DPIclimate/enviro-node/electronics/motherboard/enviro-node/parts/connectors/5-pole/2604-3105/2604-3105.stp

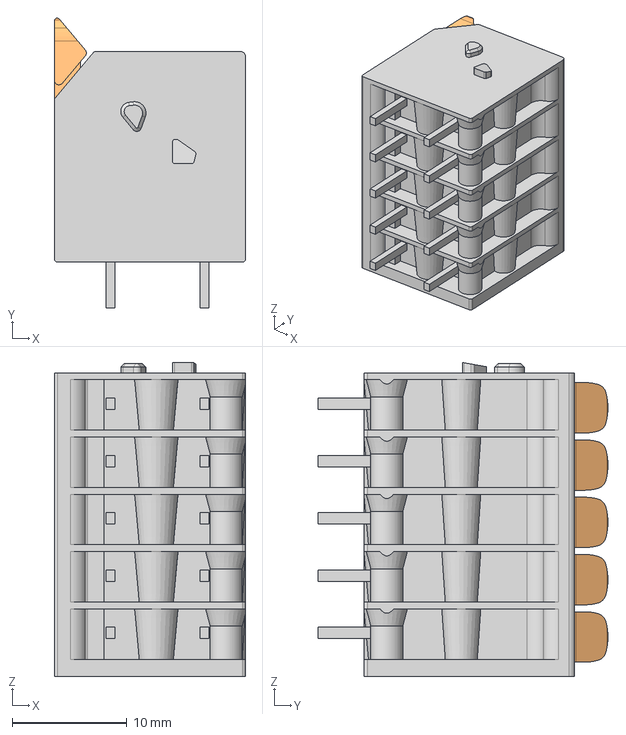
[picture p17: CAD file, 2022-11-16]
electronics/motherboard/enviro-node/parts/connectors/5-pole/2604-3105/2604-3105.stp
16.7 x 25.3 x 27.4 mm
