DPIclimate/enviro-node/electronics/motherboard/enviro-node/parts/connectors/EJ503A/EJ503A.step

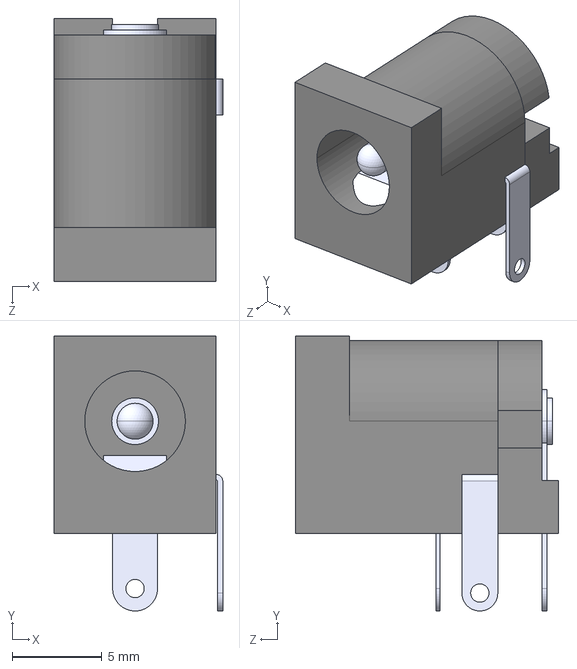
[picture p18: CAD file, 2022-09-02]
electronics/motherboard/enviro-node/parts/connectors/EJ503A/EJ503A.step
9.38 x 15.3 x 14.6 mm
