DPIclimate/enviro-node/electronics/motherboard/enviro-node/parts/connectors/jtag/3221-10-0100-00/3221-10-0100-00.STEP

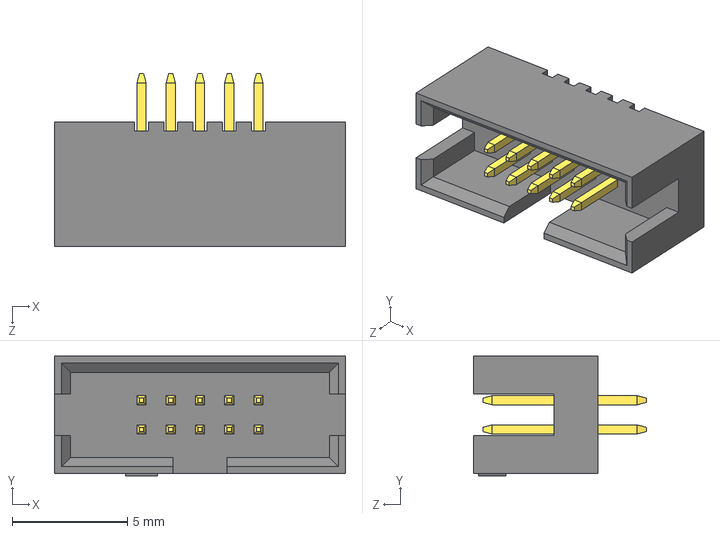
[picture p19: CAD file, 2023-01-09]
electronics/motherboard/enviro-node/parts/connectors/jtag/3221-10-0100-00/3221-10-0100-00.STEP
12.7 x 5.20 x 7.50 mm
