DPIclimate/enviro-node/electronics/motherboard/enviro-node/parts/connectors/nano-sim/SIM8060-6-0-14-00-A/SIM8060-6-0-14-00-A.stp

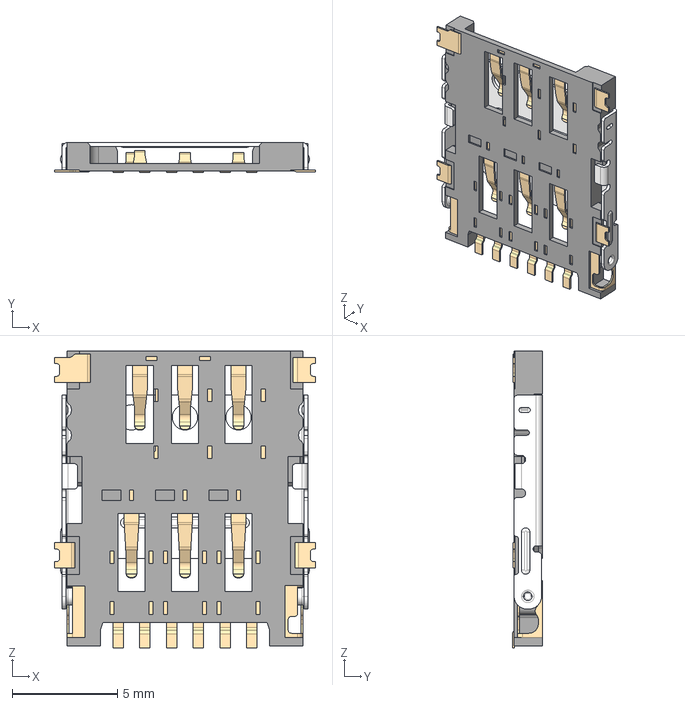
[picture p20: CAD file, 2022-10-10]
electronics/motherboard/enviro-node/parts/connectors/nano-sim/SIM8060-6-0-14-00-A/SIM8060-6-0-14-00-A.stp
12.4 x 1.43 x 14.1 mm
SIM8060-6-0-14-00-A_PART2
SIM8060-6-0-14-00-A_PART1
