DPIclimate/enviro-node/electronics/motherboard/enviro-node/parts/connectors/PCIe/MDT420B03001/MDT420B03001.step

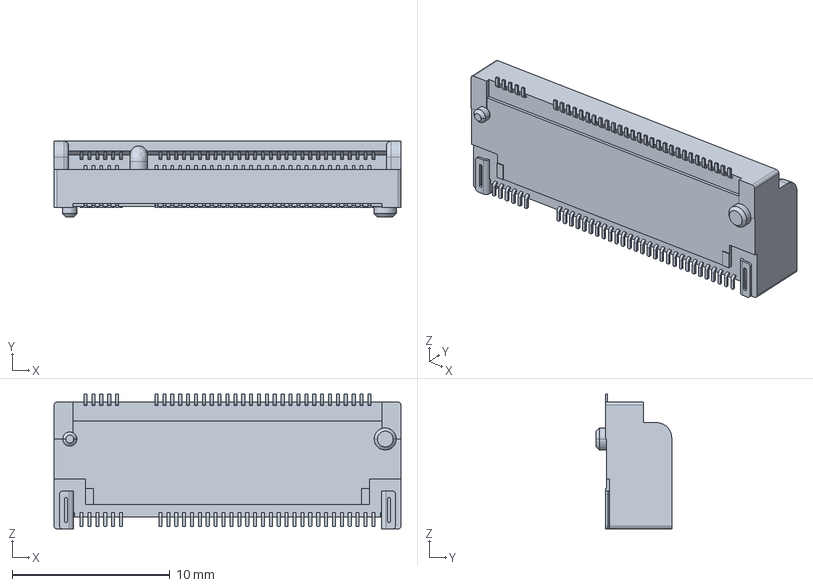
[picture p21: CAD file, 2022-09-12]
electronics/motherboard/enviro-node/parts/connectors/PCIe/MDT420B03001/MDT420B03001.step
22.0 x 4.80 x 8.55 mm
