DPIclimate/enviro-node/electronics/motherboard/enviro-node/parts/connectors/TBP02R2-381-02BE/TBP02R2-381-02BE.step

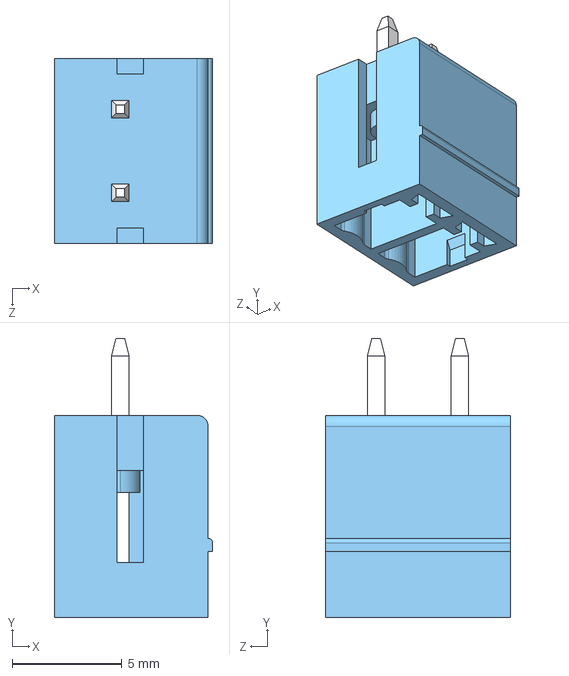
[picture p22: CAD file, 2022-09-15]
electronics/motherboard/enviro-node/parts/connectors/TBP02R2-381-02BE/TBP02R2-381-02BE.step
7.20 x 12.7 x 8.41 mm
