DPIclimate/enviro-node/electronics/motherboard/enviro-node/parts/connectors/TBP02R2-381-03BE/TBP02R2-381-03BE.step

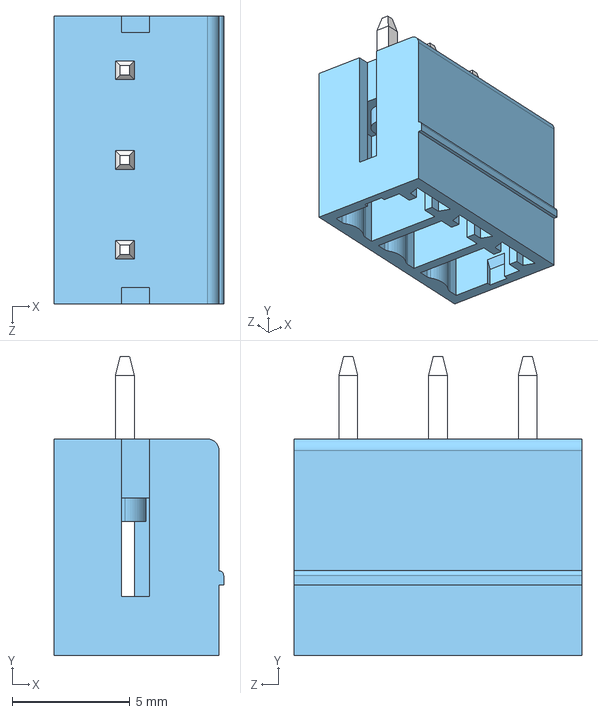
[picture p23: CAD file, 2022-09-15]
electronics/motherboard/enviro-node/parts/connectors/TBP02R2-381-03BE/TBP02R2-381-03BE.step
7.20 x 12.7 x 12.2 mm
