DPIclimate/enviro-node/electronics/motherboard/enviro-node/parts/connectors/TBP02R2-381-04BE/TBP02R2-381-04BE.step

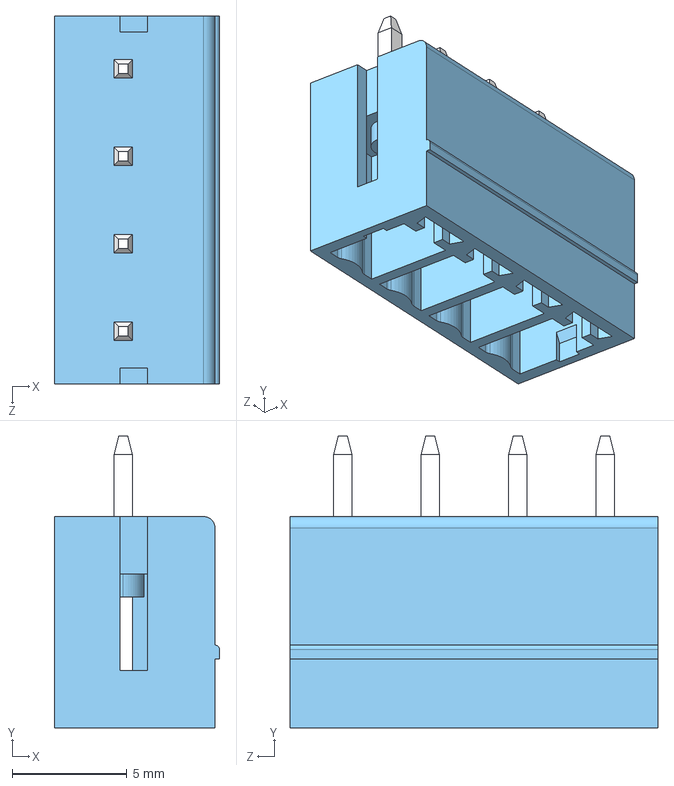
[picture p24: CAD file, 2022-09-02]
electronics/motherboard/enviro-node/parts/connectors/TBP02R2-381-04BE/TBP02R2-381-04BE.step
7.20 x 12.7 x 16.0 mm
