DPIclimate/enviro-node/electronics/motherboard/enviro-node/parts/connectors/usb-c/USB4070-30-C/USB4070-30-C.step

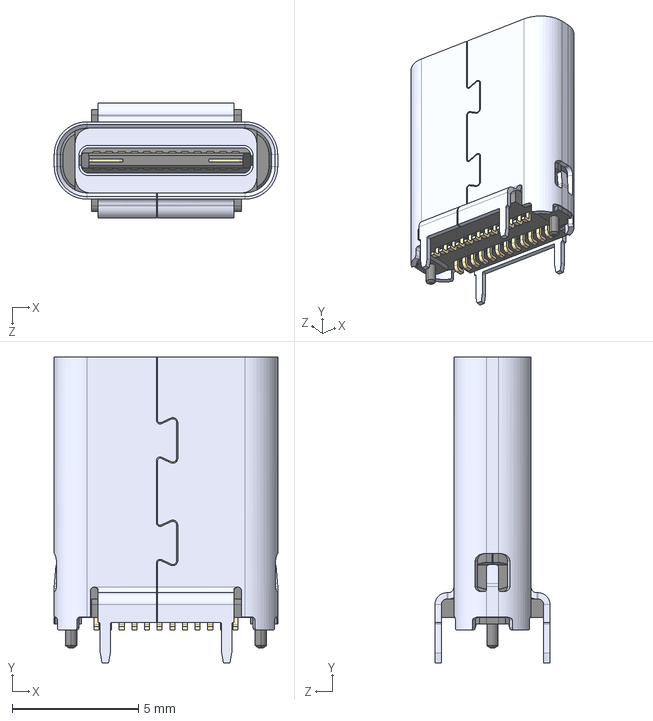
[picture p25: CAD file, 2022-09-13]
electronics/motherboard/enviro-node/parts/connectors/usb-c/USB4070-30-C/USB4070-30-C.step
8.84 x 12.1 x 4.55 mm
