DPIclimate/enviro-node/electronics/motherboard/enviro-node/parts/connectors/usb-c/USB4145-03-0230-C_REVA/USB4145-03-0070-C.stp

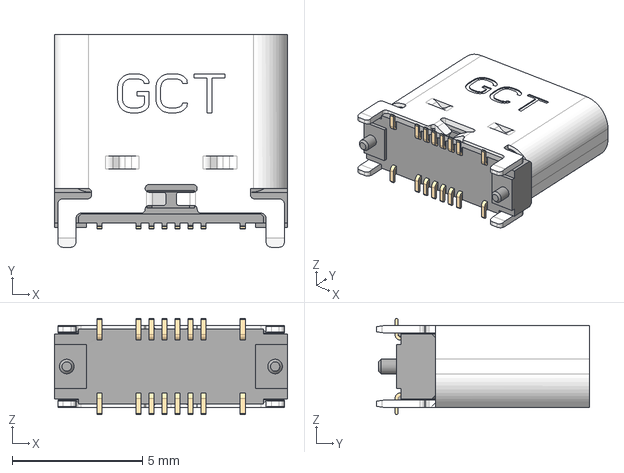
[picture p26: CAD file, 2022-10-10]
electronics/motherboard/enviro-node/parts/connectors/usb-c/USB4145-03-0230-C_REVA/USB4145-03-0070-C.stp
8.95 x 8.16 x 3.69 mm
USB4145-03-0070-C_PART2
USB4145-03-0070-C_PART1
