DPIclimate/enviro-node/electronics/motherboard/enviro-node/parts/diodes/clamping/AOZ8904CIL/SOT-23-6_AOS.step

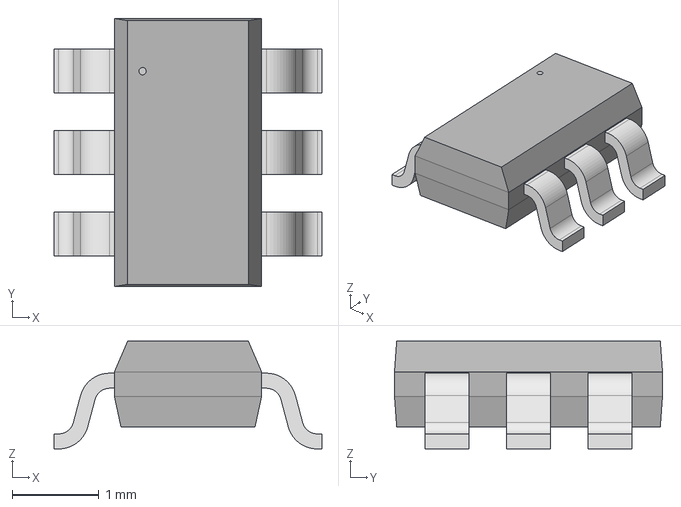
[picture p27: CAD file, 2022-10-10]
electronics/motherboard/enviro-node/parts/diodes/clamping/AOZ8904CIL/SOT-23-6_AOS.step
3.10 x 3.10 x 1.25 mm
