DPIclimate/enviro-node/electronics/motherboard/enviro-node/parts/diodes/MBRS340/MBRS340.step

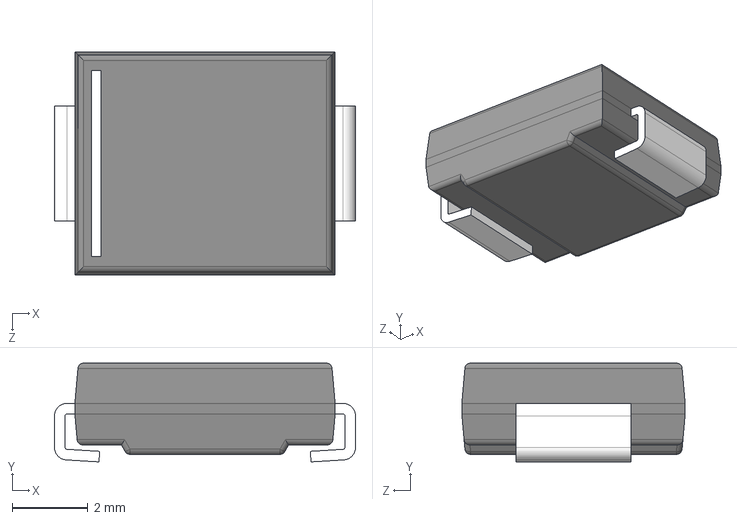
[picture p28: CAD file, 2022-09-02]
electronics/motherboard/enviro-node/parts/diodes/MBRS340/MBRS340.step
7.95 x 2.61 x 5.90 mm
