DPIclimate/enviro-node/electronics/motherboard/enviro-node/parts/diodes/SM5817PL/SODFL3718X108N.step

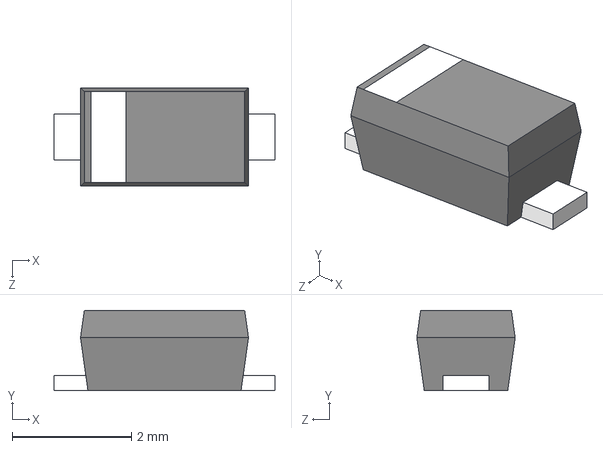
[picture p29: CAD file, 2022-09-02]
electronics/motherboard/enviro-node/parts/diodes/SM5817PL/SODFL3718X108N.step
3.71 x 1.35 x 1.65 mm
