DPIclimate/enviro-node/electronics/motherboard/enviro-node/parts/diodes/SS34LW_RVG/SS34LW_RVG.step

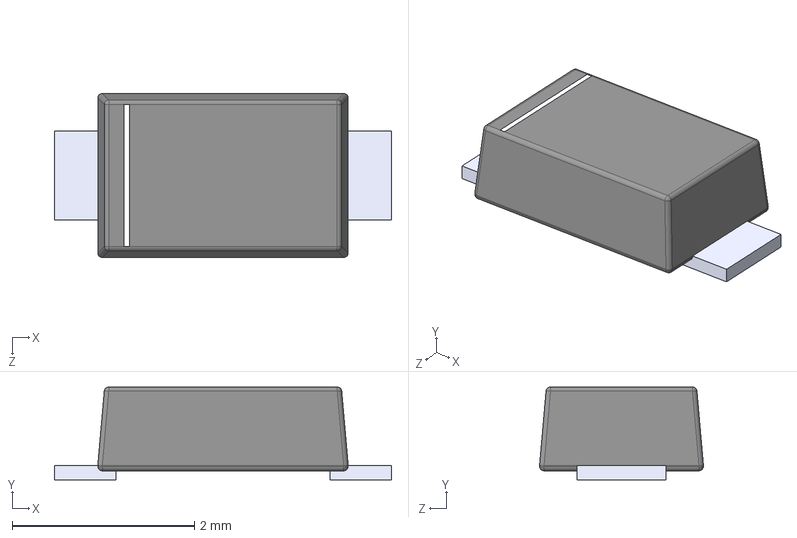
[picture p30: CAD file, 2022-09-13]
electronics/motherboard/enviro-node/parts/diodes/SS34LW_RVG/SS34LW_RVG.step
3.70 x 1.02 x 1.80 mm
