DPIclimate/enviro-node/electronics/motherboard/enviro-node/parts/ferrite-beads/FBMH2012HM221-TV/FBMH2012HM221-TV.step

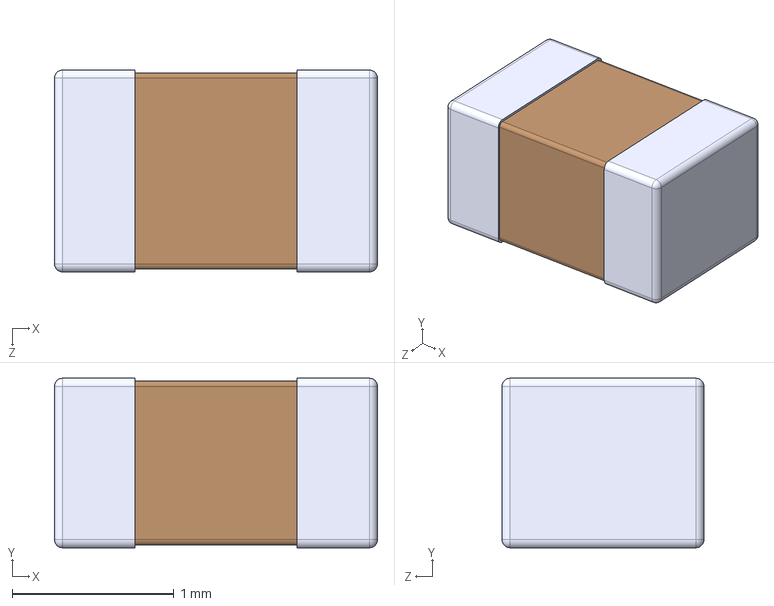
[picture p31: CAD file, 2022-10-10]
electronics/motherboard/enviro-node/parts/ferrite-beads/FBMH2012HM221-TV/FBMH2012HM221-TV.step
2.00 x 1.05 x 1.25 mm
