DPIclimate/enviro-node/electronics/motherboard/enviro-node/parts/inductors/CBC2518T100M/CBC2518T100M.step

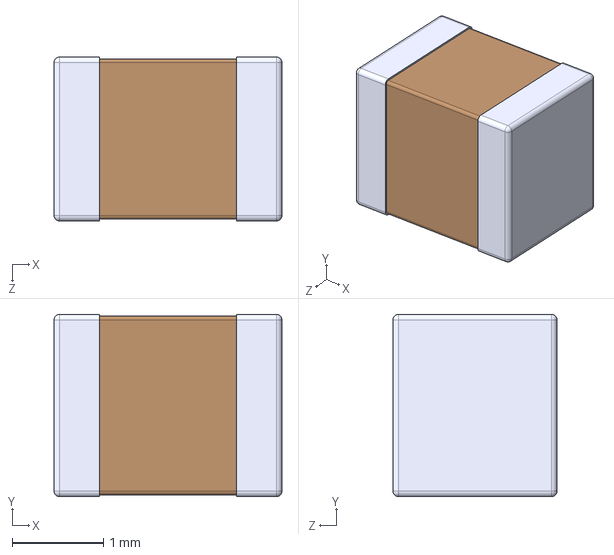
[picture p32: CAD file, 2022-09-02]
electronics/motherboard/enviro-node/parts/inductors/CBC2518T100M/CBC2518T100M.step
2.50 x 2.00 x 1.80 mm
