DPIclimate/enviro-node/electronics/motherboard/enviro-node/parts/inductors/LQH43CN100K03L/LQH43CN100K03L.step

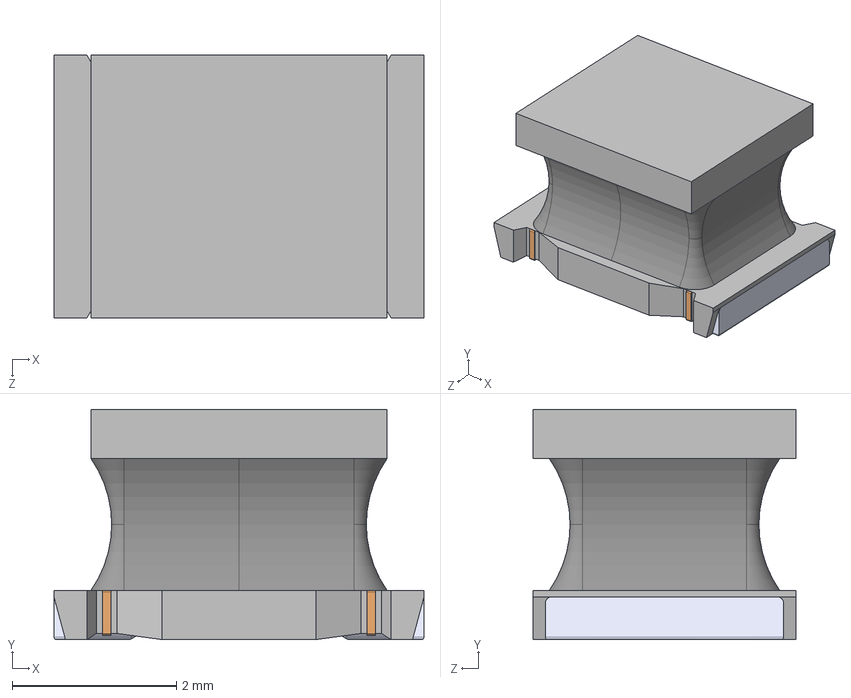
[picture p33: CAD file, 2022-10-12]
electronics/motherboard/enviro-node/parts/inductors/LQH43CN100K03L/LQH43CN100K03L.step
4.50 x 2.80 x 3.20 mm
