DPIclimate/enviro-node/electronics/motherboard/enviro-node/parts/inductors/SRP4020TA-5R6M/IND2_SRP4020TA-R56M_BRN.step

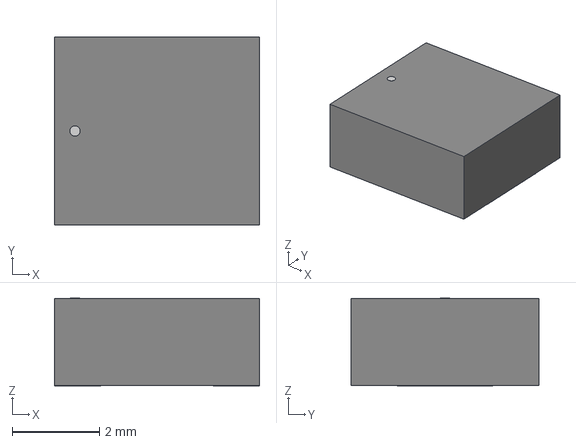
[picture p34: CAD file, 2022-11-08]
electronics/motherboard/enviro-node/parts/inductors/SRP4020TA-5R6M/IND2_SRP4020TA-R56M_BRN.step
4.70 x 4.32 x 2.01 mm
