DPIclimate/enviro-node/electronics/motherboard/enviro-node/parts/leds/BB-2020BGR-TRB/BB-2020BGR-TRB.step

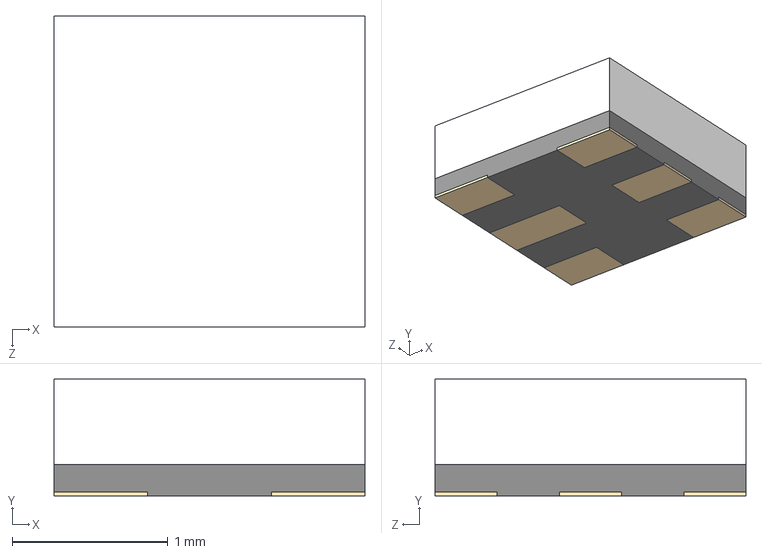
[picture p35: CAD file, 2022-09-12]
electronics/motherboard/enviro-node/parts/leds/BB-2020BGR-TRB/BB-2020BGR-TRB.step
2.00 x 0.75 x 2.00 mm
