DPIclimate/enviro-node/electronics/motherboard/enviro-node/parts/level-shifter/NVT2006PW/TSSOP16_SOT403-1_NXP.step

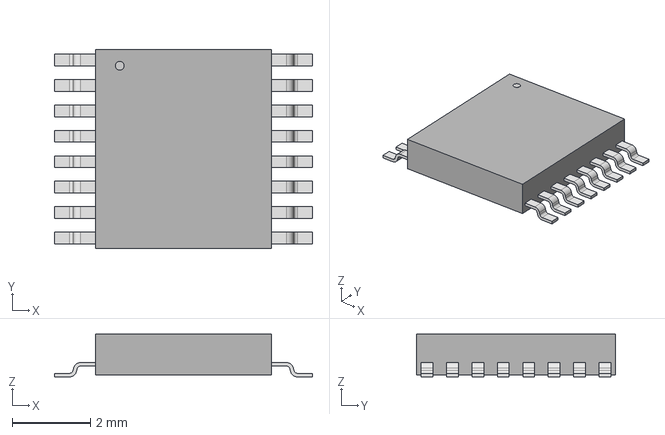
[picture p36: CAD file, 2022-10-10]
electronics/motherboard/enviro-node/parts/level-shifter/NVT2006PW/TSSOP16_SOT403-1_NXP.step
6.60 x 5.11 x 1.09 mm
