DPIclimate/enviro-node/electronics/motherboard/enviro-node/parts/microcontrollers/ESP32-WROOM-32E__16MB_/ESP32-WROOM-32E__16MB_.step

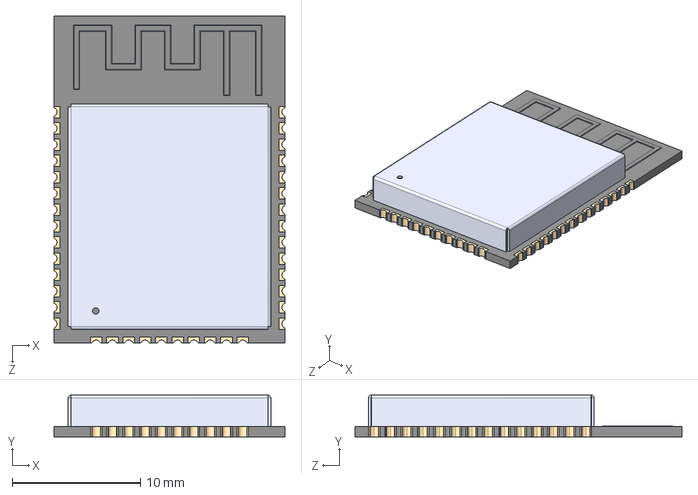
[picture p37: CAD file, 2022-11-02]
electronics/motherboard/enviro-node/parts/microcontrollers/ESP32-WROOM-32E__16MB_/ESP32-WROOM-32E__16MB_.step
18.0 x 3.25 x 25.5 mm
