DPIclimate/enviro-node/electronics/motherboard/enviro-node/parts/mosfets/p-channel/SSM3J340R-LF/SOT-23F.step

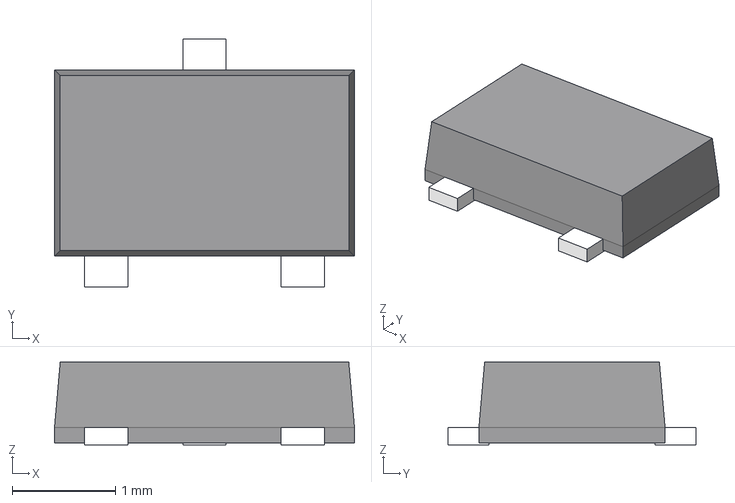
[picture p38: CAD file, 2023-01-09]
electronics/motherboard/enviro-node/parts/mosfets/p-channel/SSM3J340R-LF/SOT-23F.step
2.90 x 2.40 x 0.8 mm
