DPIclimate/enviro-node/electronics/motherboard/enviro-node/parts/ocillators/ABS05-32.768KHZ-9-T/ABS05-32.768KHZ-9-T.step

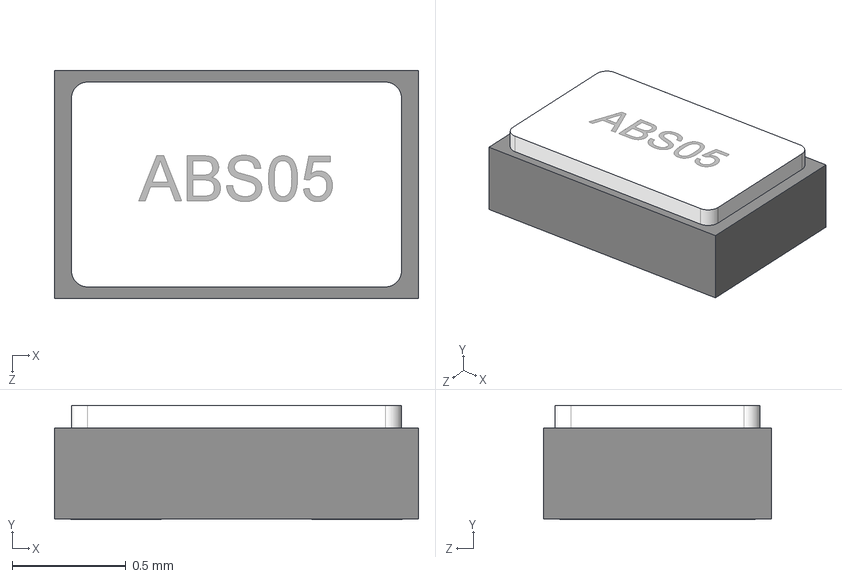
[picture p39: CAD file, 2022-09-12]
electronics/motherboard/enviro-node/parts/ocillators/ABS05-32.768KHZ-9-T/ABS05-32.768KHZ-9-T.step
1.60 x 0.503 x 1.00 mm
