DPIclimate/enviro-node/electronics/motherboard/enviro-node/parts/ocillators/ABS07AIG-32.768KHZ-T/ABS07AIG-32.768KHZ-T.step

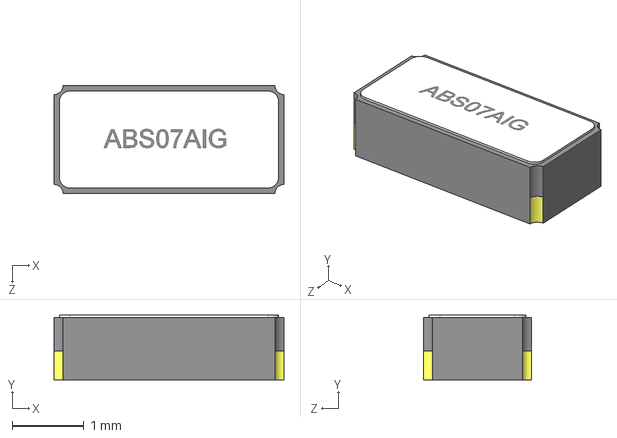
[picture p40: CAD file, 2022-11-02]
electronics/motherboard/enviro-node/parts/ocillators/ABS07AIG-32.768KHZ-T/ABS07AIG-32.768KHZ-T.step
3.20 x 0.901 x 1.50 mm
