DPIclimate/enviro-node/electronics/motherboard/enviro-node/parts/piezo-buzzers/PS1240P02BT/PS1240P02BT.step

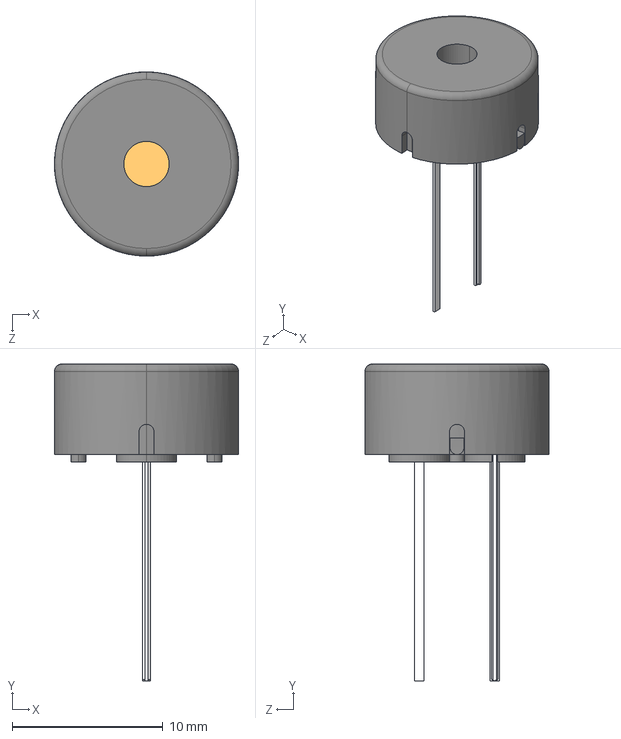
[picture p41: CAD file, 2022-11-02]
electronics/motherboard/enviro-node/parts/piezo-buzzers/PS1240P02BT/PS1240P02BT.step
12.2 x 21.0 x 12.2 mm
