DPIclimate/enviro-node/electronics/motherboard/enviro-node/parts/switches/dip/DS04-254-2-02BK-SMT/DS04-254-2-02BK-SMT.step

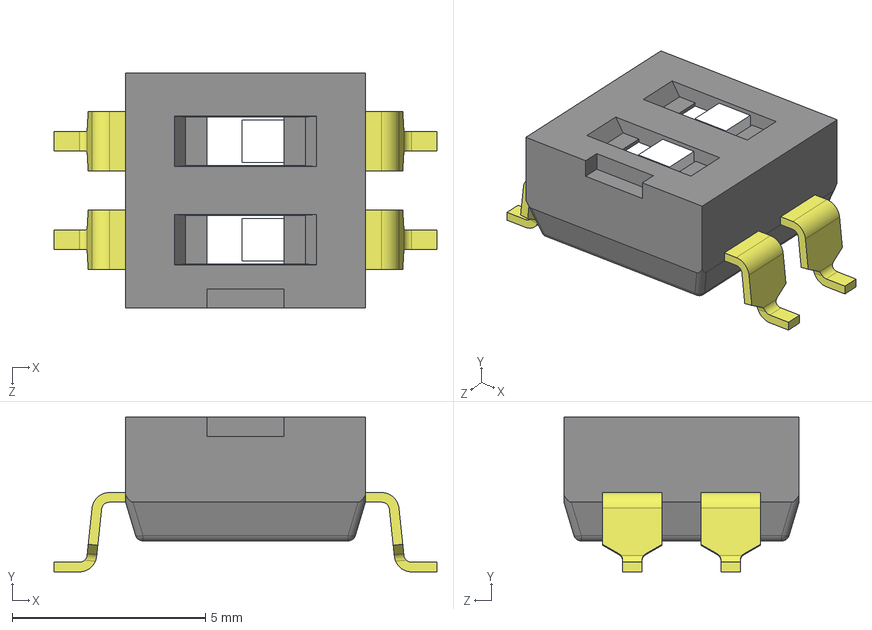
[picture p42: CAD file, 2022-09-13]
electronics/motherboard/enviro-node/parts/switches/dip/DS04-254-2-02BK-SMT/DS04-254-2-02BK-SMT.step
9.90 x 4.00 x 6.08 mm
