DPIclimate/enviro-node/electronics/motherboard/enviro-node/parts/transistors/AOD417/AOD417.step

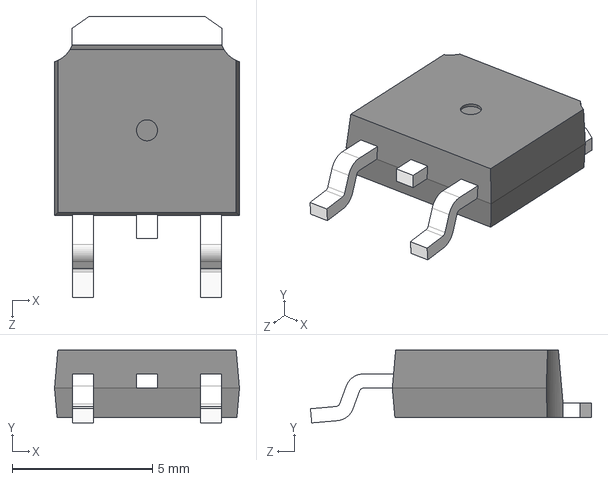
[picture p43: CAD file, 2022-09-02]
electronics/motherboard/enviro-node/parts/transistors/AOD417/AOD417.step
6.60 x 2.60 x 10.0 mm
