DPIclimate/enviro-node/electronics/motherboard/enviro-node/parts/voltage-regulators/MIC2145BMM/MIC2145BMM.step

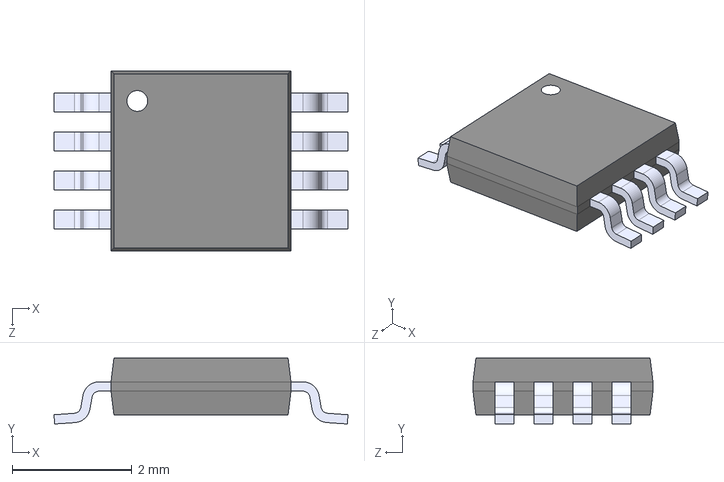
[picture p44: CAD file, 2022-09-02]
electronics/motherboard/enviro-node/parts/voltage-regulators/MIC2145BMM/MIC2145BMM.step
4.90 x 1.10 x 3.00 mm
