DPIclimate/enviro-node/electronics/motherboard/enviro-node/parts/voltage-regulators/MIC2288YD5-TR/MIC2288YD5-TR.step

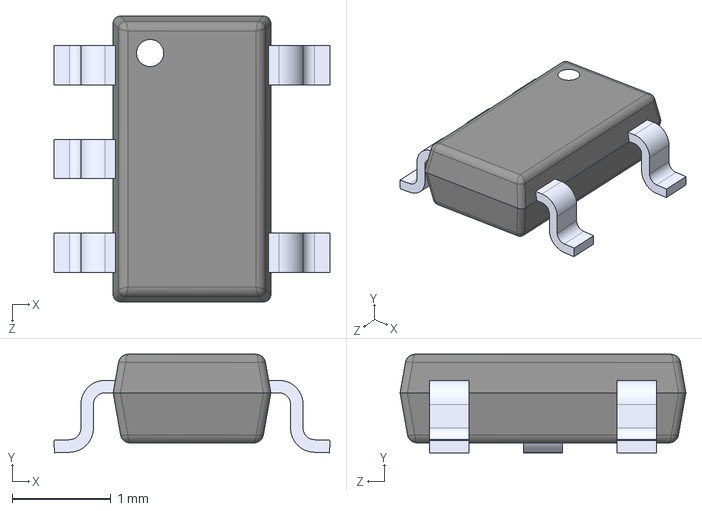
[picture p45: CAD file, 2022-10-12]
electronics/motherboard/enviro-node/parts/voltage-regulators/MIC2288YD5-TR/MIC2288YD5-TR.step
2.80 x 1.00 x 2.90 mm
