DPIclimate/enviro-node/electronics/motherboard/enviro-node/parts/voltage-regulators/XC6215B332MR-G/SOT-25_TOR.step

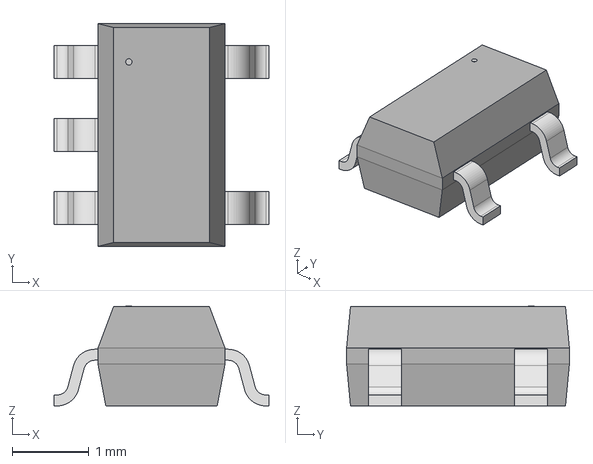
[picture p46: CAD file, 2022-11-02]
electronics/motherboard/enviro-node/parts/voltage-regulators/XC6215B332MR-G/SOT-25_TOR.step
2.79 x 2.90 x 1.30 mm
