DPIclimate/enviro-node/cad/PVC WB board holder final.stl

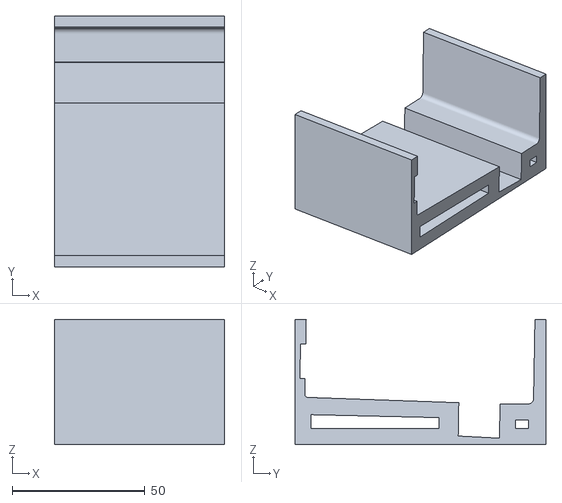
[picture p47: CAD file, 2023-05-02]
cad/PVC WB board holder final.stl
64.0 x 94.3 x 47.2
