DPIclimate/enviro-node/cad/Breakoutbox holder Final.stl

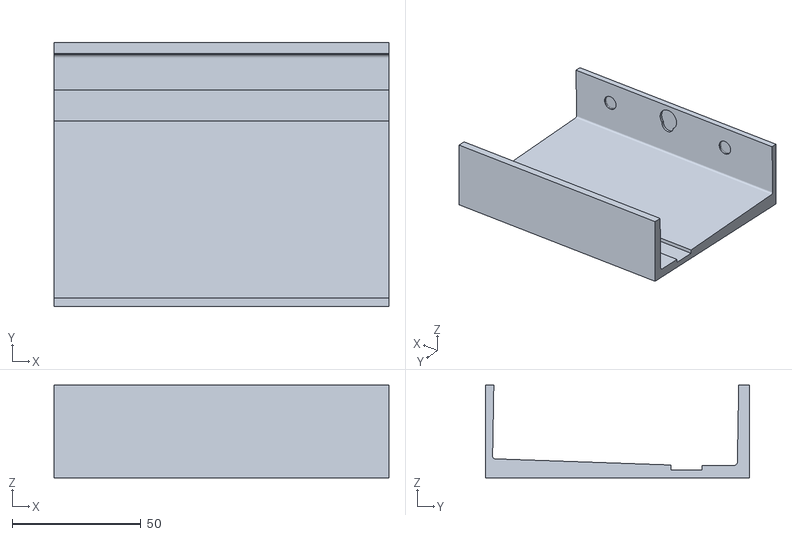
[picture p48: CAD file, 2023-05-02]
cad/Breakoutbox holder Final.stl
130.0 x 102.6 x 36.0
