DPIclimate/enviro-node/firmware/wombat/src/ntp.cpp

#include <Arduino.h>
#include <time.h> // Note: this is the standard c time library, not Time.h
#include "SparkFun_u-blox_SARA-R5_Arduino_Library.h"

#define TAG "ntp"

// Get the time from NTP
// This code is based heavily on:
// https://docs.arduino.cc/tutorials/mkr-nb-1500/mkr-nb-library-examples#mkr-nb-gprs-udp-ntp-client
// Many thanks to: Michael Margolis, Tom Igoe, Arturo Guadalupi, et al

// NTP Server
const char* ntpServer = "au.pool.ntp.org";               // The Network Time Protocol Server
//const char* ntpServer = "africa.pool.ntp.org";        // The Network Time Protocol Server
//const char* ntpServer = "asia.pool.ntp.org";          // The Network Time Protocol Server
//const char* ntpServer = "europe.pool.ntp.org";        // The Network Time Protocol Server
//const char* ntpServer = "north-america.pool.ntp.org"; // The Network Time Protocol Server
//const char* ntpServer = "oceania.pool.ntp.org";       // The Network Time Protocol Server
//const char* ntpServer = "south-america.pool.ntp.org"; // The Network Time Protocol Server

//=-=-=-=-=-=-=-=-=-=-=-=-=-=-=-=-=-=-=-=-=-=-=-=-=-=-=-=-=-=-=-=-=-=-=-=-=-=-=-=-=-=-=-=-=

bool getNTPTime(SARA_R5 &r5) {
    int serverPort = 123; //NTP requests are to port 123

    // Set up the packetBuffer for the NTP request
    const int NTP_PACKET_SIZE = 48; // NTP time stamp is in the first 48 bytes of the message
    byte packetBuffer[NTP_PACKET_SIZE]; //buffer to hold incoming and outgoing packets

    // set all bytes in the buffer to 0
    memset(packetBuffer, 0, NTP_PACKET_SIZE);

    // Initialize values needed to form NTP request. The client request only needs to set version numbers & mode.
    packetBuffer[0]  = 0b00000000;  // LI 0
    packetBuffer[0] |= 0b00100000;  // Version 4
    packetBuffer[0] |= 0b00000011;  // Mode 3, client
    //=-=-=-=-=-=-=-=-=-=-=-=-=-=-=-=-=-=-=-=-=-=-=-=-=-=-=-=-=-=-=-=-=-=-=-=-=-=-=-=-=-=-=-=-=

    // Allocate a UDP socket to talk to the NTP server

    int socketNum = r5.socketOpen(SARA_R5_UDP);
    if (socketNum == -1) {
        ESP_LOGE(TAG, "socketOpen failed");
        return false;
    }

    ESP_LOGI(TAG, "using socket %u", socketNum);

    //=-=-=-=-=-=-=-=-=-=-=-=-=-=-=-=-=-=-=-=-=-=-=-=-=-=-=-=-=-=-=-=-=-=-=-=-=-=-=-=-=-=-=-=-=

    // Send the request - NTP uses UDP

    if (r5.socketWriteUDP(socketNum, ntpServer, serverPort, (const char *)&packetBuffer, NTP_PACKET_SIZE) != SARA_R5_SUCCESS) {
        ESP_LOGE(TAG, "socketWrite failed");
        r5.socketClose(socketNum); // Be nice. Close the socket
        return false;
    }

    // Wait up to 10 seconds for the response
    unsigned long requestTime = millis();

    // (millis() - start) < timeout
    while ((millis() - requestTime) < 10000) {
        int avail = 0;
        if (r5.socketReadAvailableUDP(socketNum, &avail) != SARA_R5_SUCCESS) {
            ESP_LOGE(TAG, "socketReadAvailable failed");
            r5.socketClose(socketNum);
            return false;
        }

        if (avail >= NTP_PACKET_SIZE) {
            if (avail > NTP_PACKET_SIZE) {
                ESP_LOGW(TAG, "Too much data received: %d. Expected: %d", avail, NTP_PACKET_SIZE);
            }

            if (r5.socketReadUDP(socketNum, NTP_PACKET_SIZE, (char *)&packetBuffer) != SARA_R5_SUCCESS) {
                ESP_LOGE(TAG, "socketRead failed");
                r5.socketClose(socketNum); // Be nice. Close the socket
                return false;
            }

            Serial.println();
            Serial.println("NTP response");

            int x = 0;
            char hexbuf[5]; // Also used to print reference id field, so 5 long.
            while (x < NTP_PACKET_SIZE) {
                snprintf(hexbuf, sizeof(hexbuf), "%02X ", packetBuffer[x++]);
                Serial.print(hexbuf);
                if (x % 16 == 0) {
                    Serial.println();
                }
            }
/*
 0: 24 02 06 E7
 4: 00 00 00 3C
 8: 00 00 00 28
12: 5C 15 35 D9
16: E7 8B F7 38 2B DC 93 DD
24: 00 00 00 00 00 00 00 00
32: E7 8B F8 61 6B 17 77 A0
40: E7 8B F8 61 6B 17 F3 80

 */

            // A stratum value of 0 or 1 means a reference id field will also be present, so print that out for
            // debugging, and if statum is 0, do not try to set the time because that's an error indicator.
            if (packetBuffer[1] < 2) {
                hexbuf[0] = packetBuffer[12];
                hexbuf[1] = packetBuffer[13];
                hexbuf[2] = packetBuffer[14];
                hexbuf[3] = packetBuffer[15];
                hexbuf[4] = 0;

                ESP_LOGI(TAG, "NTP Ref Id: %s", hexbuf);

                if (packetBuffer[1] == 0) {
                    ESP_LOGE(TAG, "NTP KoD");
                    return false;
                }
            }

            // Extract the time from the reply

            // The timestamp starts at byte 40 of the received packet and is a uint32_t value.

            unsigned long highWord = word(packetBuffer[40], packetBuffer[41]);
            unsigned long lowWord = word(packetBuffer[42], packetBuffer[43]);

            // combine the four bytes (two words) into a long integer
            // this is NTP time (seconds since Jan 1 1900):
            unsigned long secsSince1900 = highWord << 16 | lowWord;

            ESP_LOGI(TAG, "seconds since Jan 1 1900 = %lu", secsSince1900);

            // now convert NTP time into everyday time:
            // Unix time starts on Jan 1 1970. In seconds, that's 2208988800:
            const unsigned long seventyYears = 2208988800UL;

            // subtract seventy years:
            unsigned long epoch = secsSince1900 - seventyYears;

            ESP_LOGI(TAG, "Unix epoch = %lu", epoch);

            setenv("TZ", "UTC", 1);
            tzset();

            struct timeval tv;

            tv.tv_sec = epoch; //dateTime;
            tv.tv_usec = 0;

            settimeofday(&tv, nullptr);

            // Instead of calculating the year, month, day, etc. manually, let's use time_t and tm to do it for us!
            time_t dateTime = epoch;
            tm *theTime = gmtime(&dateTime);

            // Load the time into y, mo, d, h, min, s
            int y = theTime->tm_year - 100; // tm_year is years since 1900. Convert to years since 2000.
            int mo = theTime->tm_mon + 1; //tm_mon starts at zero. Add 1 for January.

            ESP_LOGI(TAG, "Now = %4d/%02d/%02d %02d:%02d:%02d", y, mo, theTime->tm_mday, theTime->tm_hour, theTime->tm_min, theTime->tm_sec);

            //Set the SARA's RTC. Set the time zone to zero so the clock uses UTC
            if (r5.setClock(y, mo, theTime->tm_mday, theTime->tm_hour, theTime->tm_min, theTime->tm_sec, 0) != SARA_R5_SUCCESS) {
                ESP_LOGE(TAG, "SARA R5 setClock failed");
            }

            r5.socketClose(socketNum); // Be nice. Close the socket
            return (true); // We are done!
        }

        delay(100); // Wait before trying again
    }

    //=-=-=-=-=-=-=-=-=-=-=-=-=-=-=-=-=-=-=-=-=-=-=-=-=-=-=-=-=-=-=-=-=-=-=-=-=-=-=-=-=-=-=-=-=

    ESP_LOGW(TAG, "no NTP data received");
    r5.socketClose(socketNum); // Be nice. Close the socket
    return false;
}
